souliss/smart-thermostat/Libraries-Core-Docs/docs/11448259.png

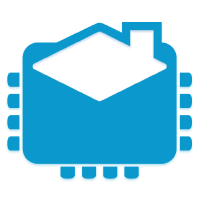
Libraries-Core-Docs/docs/11448259.png
