souliss/smart-thermostat/Libraries-Core-Docs/MOSTRINA_3D/Prototipo.png

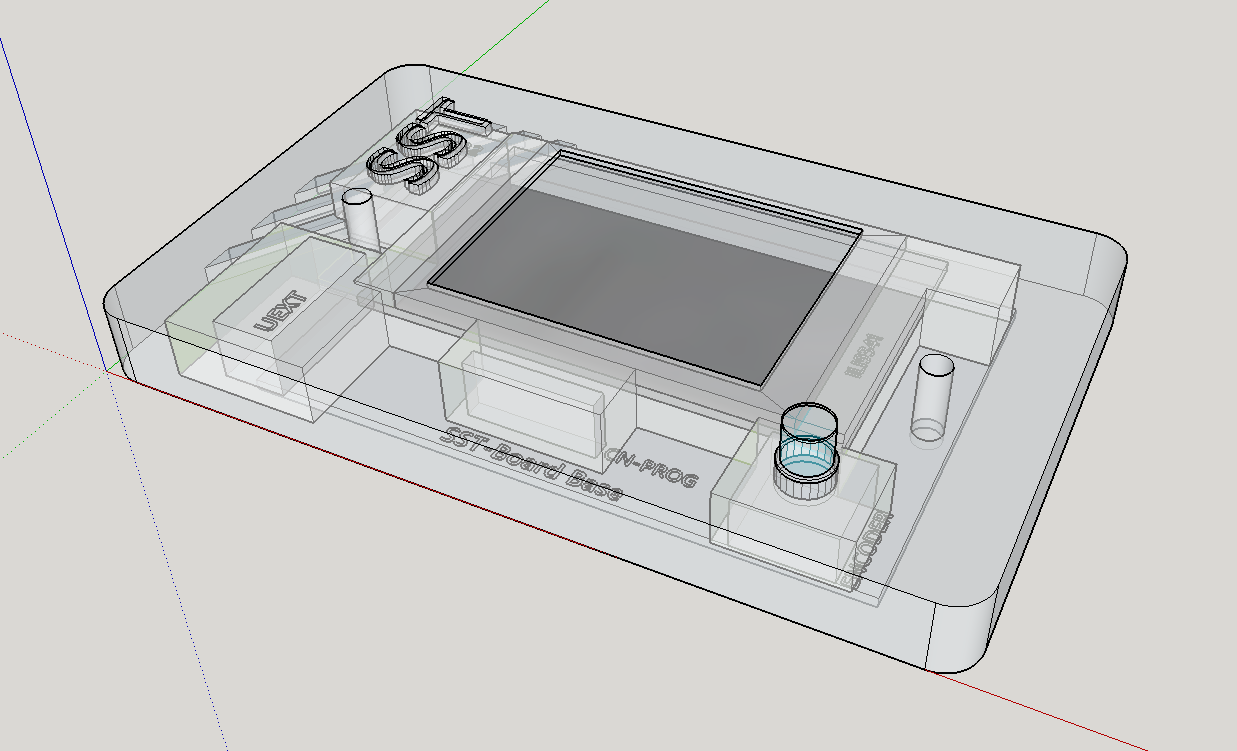
Libraries-Core-Docs/MOSTRINA_3D/Prototipo.png
