souliss/smart-thermostat/Libraries-Core-Docs/howto_program.png

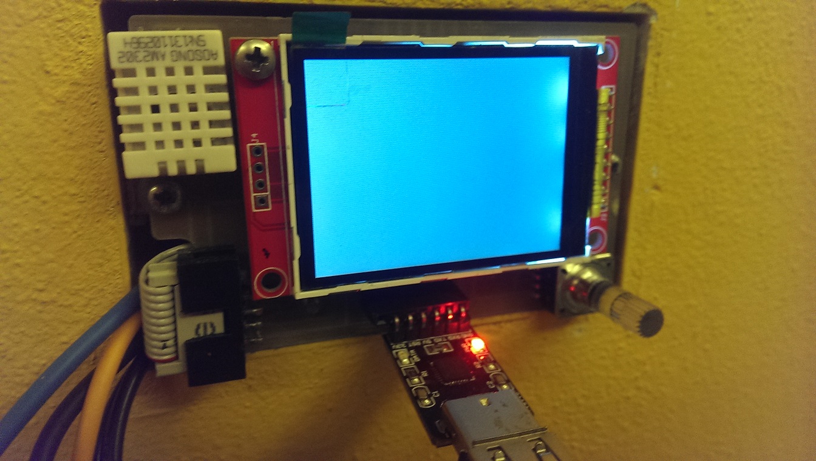
Libraries-Core-Docs/howto_program.png
